Mykhailo-Sichkaruk/PRJ-PENDING-GestureGlove/content/docs/sk/sthdf/ST-029-MarochokYaroslav/index.md

---
title: "ST-029-MarochokYaroslav"
---

# Yaroslav Marochok

Identifikátor v zozname: **ST029**. Tímový projekt: [Gesture Glove](../PRJ-PENDING-GestureGlove/index.md).

- [About Me](./about-me/index.md)
- [Knowledge Contribution (KNIFE)](./knowledge-contribution/index.md)
- [Project Summary](./project-summary/index.md)
- [Project Outcomes](./project-outcomes/index.md)
- [Pitch Presentation](./pitch-presentation/index.md)
- [Final Presentation](./final-presentation/index.md)
- [Reflexia](./reflexia/index.md)

Pripravená štruktúra pre individuálne výstupy. Autor doplní vlastný text; príspevky ani výsledky zatiaľ nie sú deklarované.

GitHub: [ymarochok](https://github.com/ymarochok).
