Mykhailo-Sichkaruk/PRJ-PENDING-GestureGlove/core/templates/content/sthdf/body/index.md

# STHDF — Dashboard

V tejto sekcii sa nachádzajú študentské deliverables.

## 🔗 Navigácia

- **01 – About Me**  
  → [01 – About Me](./students/about-me/index.md)
  
- **02 – Knowledge Contribution (A2)**  
  → [02 – Knowledge Contribution (A2)](./students/knowledge-contribution/index.md)

- **03 – Project Summary**  
  → [03 – Project Summary](./students/project-summary/index.md)

- **04 – Project Outcomes**  
  → [04 – Project Outcomes](./students/project-outcomes/index.md)

- **05 – Pitch Presentation**  
  → [05 – Pitch Presentation](./students/pitch-presentation/index.md)

- **06 – Final Presentation**  
  → [06 – Final Presentation](./students/final-presentation/index.md)

- **07 – Reflexia**  
  → [07 – Reflexia](./students/reflexia/index.md)

---

## ℹ️ Poznámka
Tento súbor je súčasťou *defaultného template* a zabezpečuje stabilitu sidebaru aj navigácie.

## Navigácia
- [↩️ Späť](../../index.md)
- [Projektové rámce — 7Ds, SDLC, Q12](./projects/index.md)
