Mykhailo-Sichkaruk/PRJ-PENDING-GestureGlove/content/docs/en/knifes/knifes_overview/KNIFE_Overview_List.md

---
# 🧩 Versioning – systém dopĺňa automaticky
fm_version: "1.0.1"

# Dátum buildu – generuje skript
fm_build: "{{FM_BUILD}}"

# Poznámka k verzii – voliteľné
fm_version_comment: ""

# 🆔 IDENTITY --------------------------------------------------------

# ID generuje CLI / skript
id: "KNIFE_OVERVIEW_LIST_EN"

# Unikátne UUID – generuje skript
guid: "47377b57-1a6c-4d85-b179-e202dff15484"

# 🧭 CONTEXT ---------------------------------------------------------

# DAO / doména (knife, sdlc, q12, 7ds...) dopĺňa skript
dao: "{{DAO}}"

# Názov zápisu – dopĺňa používateľ
title: "🗂 KNIFE Overview – List"

# Krátky popis – dopĺňa používateľ (voliteľné)
description: "{{DESCRIPTION}}"

# 👥 AUTHORSHIP ------------------------------------------------------

# Hlavný autor – z globálneho configu
author: "Roman Kazička"

# Zoznam autorov – generuje skript
authors:
  - "Roman Kazička"

# 🗂 CLASSIFICATION ---------------------------------------------------

# Nadradená kategória – môže doplniť používateľ
category: ""

# Typ dokumentu (guide, case, tutorial...) – používateľ (voliteľné)
type: ""

# Priorita (low/medium/high) – voliteľné
priority: ""

# Tagy – odporúča sa 2–6 tagov.
# Typy tagov:
#   - rámce: knife, 7ds, sdlc, q12
#   - účel: tutorial, guide, pattern, case-study
#   - téma: git, backup, ai, communication
#   - úroveň: beginner, intermediate, advanced
tags: []

# 🌍 LOCALIZATION -----------------------------------------------------

# Jazyk dokumentu – doplní skript podľa štruktúry
locale: "en"

# 🕒 LIFECYCLE --------------------------------------------------------

# Dátum vytvorenia – generuje skript
created: "2026-10-08"

# Dátum poslednej úpravy – dopĺňa človek
modified: ""

# Stav dokumentu – default "backlog"
status: "backlog"

# Viditeľnosť – default "public"
privacy: "public"

# ⚖ INTELLECTUAL PROPERTY -------------------------------------------

# Držiteľ práv k obsahu – dopĺňa skript
rights_holder_content: "Roman Kazička"

# Systémový vlastník práv
rights_holder_system: "CAA / KNIFE / LetItGrow"

# Licencia
license: "CC-BY-NC-SA-4.0"

# Disclaimer
disclaimer: "Use at your own risk. Methods provided as-is; participation is voluntary and context-aware."

# Copyright
copyright: "© 2025 Roman Kazička"

# 🔗 ORIGIN / PROVENANCE ---------------------------------------------

# Repozitár pôvodu
origin_repo: ""

# URL pôvodného repozitára
origin_repo_url: ""

# Commit pôvodu
origin_commit: ""

# Branch pôvodu
origin_branch: ""

# Systém pôvodu (CAA/KNIFE/STHDF…)
origin_system: "CAA"

# Pôvodný autor
origin_author: "Roman Kazička"

# Importovaný zdroj
origin_imported_from: ""

# Dátum importu
origin_import_date: ""

# 🧱 RESERVED ---------------------------------------------------------

fm_reserved1: ""
fm_reserved2: ""
---

# 🗂 KNIFE Overview – List

<!-- fm-visible: start -->
> **GUID:** `47377b57-1a6c-4d85-b179-e202dff15484`
> **Status:** `backlog` · **Author:** Roman Kazička · **License:** CC-BY-NC-SA-4.0
<!-- fm-visible: end -->

[📰 Blog](./KNIFE_Overview_Blog.md) | **[🗂 List](./KNIFE_Overview_List.md)** | [📊 Details](./KNIFE_Overview_Details.md) | [↩️ KNIFES](../index.md)
