Mykhailo-Sichkaruk/PRJ-PENDING-GestureGlove/content/docs/sk/sthdf/PRJ-PENDING-GestureGlove/projects/sdlc/01-Requirements/index.md

---
# 🧩 Versioning – systém dopĺňa automaticky
fm_version: "1.0.1"

# Dátum buildu – generuje skript
fm_build: "2026-10-08T11:14:47.749154+00:00"

# Poznámka k verzii – voliteľné
fm_version_comment: ""

# 🆔 IDENTITY --------------------------------------------------------

# ID generuje CLI / skript

# Unikátne UUID – generuje skript
guid: "9a84ae6a-37f9-47a1-815a-2adfdcadd318"

# 🧭 CONTEXT ---------------------------------------------------------

# DAO / doména (knife, sdlc, q12, 7ds...) dopĺňa skript
dao: "sthdf"

# Názov zápisu – dopĺňa používateľ
title: "01 Requirements"

# Krátky popis – dopĺňa používateľ (voliteľné)
description: "{{DESCRIPTION}}"

# 👥 AUTHORSHIP ------------------------------------------------------

# Hlavný autor – z globálneho configu
author: "Roman Kazicka"

# Zoznam autorov – generuje skript
authors:
  - "Roman Kazicka"

# 🗂 CLASSIFICATION ---------------------------------------------------

# Nadradená kategória – môže doplniť používateľ
category: ""

# Typ dokumentu (guide, case, tutorial...) – používateľ (voliteľné)
type: ""

# Priorita (low/medium/high) – voliteľné
priority: ""

# Tagy – odporúča sa 2–6 tagov.
# Typy tagov:
#   - rámce: knife, 7ds, sdlc, q12
#   - účel: tutorial, guide, pattern, case-study
#   - téma: git, backup, ai, communication
#   - úroveň: beginner, intermediate, advanced
tags: []

# 🌍 LOCALIZATION -----------------------------------------------------

# Jazyk dokumentu – doplní skript podľa štruktúry
locale: "sk"

# 🕒 LIFECYCLE --------------------------------------------------------

# Dátum vytvorenia – generuje skript
created: "2026-10-08 13:14"

# Dátum poslednej úpravy – dopĺňa človek
modified: "2026-10-08 13:14"

# Stav dokumentu – default "backlog"
status: "backlog"

# Viditeľnosť – default "public"
privacy: "public"

# ⚖ INTELLECTUAL PROPERTY -------------------------------------------

# Držiteľ práv k obsahu – dopĺňa skript
rights_holder_content: "Roman Kazicka"

# Systémový vlastník práv
rights_holder_system: "CAA / KNIFE / LetItGrow"

# Licencia
license: "CC-BY-NC-SA-4.0"

# Disclaimer
disclaimer: "Use at your own risk. Methods provided as-is; participation is voluntary and context-aware."

# Copyright
copyright: "© 2025 Roman Kazicka"

# 🔗 ORIGIN / PROVENANCE ---------------------------------------------

# Repozitár pôvodu
origin_repo: ""

# URL pôvodného repozitára
origin_repo_url: ""

# Commit pôvodu
origin_commit: ""

# Branch pôvodu
origin_branch: ""

# Systém pôvodu (CAA/KNIFE/STHDF…)
origin_system: "CAA"

# Pôvodný autor
origin_author: "Roman Kazicka"

# Importovaný zdroj
origin_imported_from: ""

# Dátum importu
origin_import_date: ""

# 🧱 RESERVED ---------------------------------------------------------

fm_reserved1: ""
fm_reserved2: ""
---

<!-- SDLC_INSTANCE_ID: PRJ-PENDING-GestureGlove -->

# # 01 Requirements

Zachytenie potrieb, cieľov a očakávaní používateľov. Pridaj user stories a nefunkčné požiadavky.

---
**Navigation:** [⬆️ Up](../index.md) · [🏠 Home](../index.md)
