Mykhailo-Sichkaruk/PRJ-PENDING-GestureGlove/content/docs/index.md

---
fm_version: "1.0.1"
fm_build: "2025-10-28T00:00:00Z"
fm_version_comment: "Stabilné ID/slug pre navigáciu (hub + SK + EN)"
id: "KNIFE_HOME"
guid: "4e609387-282e-5744-97f0-e5bb625100ad"
dao: "knife"
title: "KNIFE – Hub"
description: "Vstupná stránka: preklik na SK a EN dokumentáciu."
author: "Roman Kazička"
authors: ["Roman Kazička"]
category: ""
type: ""
priority: "no"
tags: []
locale: "sk"
created: "2025-10-28"
modified: "YYYY-MM-DDTHH:MM:SSZ"
status: "draft"
privacy: "public"
rights_holder_content: "Roman Kazička"
rights_holder_system: "Roman Kazička (CAA/KNIFE/LetItGrow)"
license: "CC-BY-NC-SA-4.0"
disclaimer: "Use at your own risk. Methods provided as-is; participation is voluntary and context-aware."
copyright: "© 2025 Roman Kazička / SystemThinking"
origin_repo: ""
origin_repo_url: ""
origin_commit: ""
origin_system: ""
author_id: ""
author_did: ""
fm_reserved1: ""
fm_reserved2: ""
slug: "/"
sidebar_position: "1"
---
# KNIFE – Hub

Vitaj v KNIFE dokumentácii. Vyber si jazyk:

- 🇸🇰 **Slovensky** → [/sk/](./sk/index.md)
- 🇬🇧 **English** → [/en/](./en/index.md)

## Gesture Glove — SMVIT 2026–2027

- [Tímový projekt](./sk/sthdf/PRJ-PENDING-GestureGlove/index.md)
- [Mykhailo Sichkaruk — ST033](./sk/sthdf/ST-033-SichkarukMykhailo/index.md)
- [Yaroslav Marochok — ST029](./sk/sthdf/ST-029-MarochokYaroslav/index.md)
