Mykhailo-Sichkaruk/PRJ-PENDING-GestureGlove/content/docs/sk/index.md

---
fm_version: "1.0.1"
fm_build: "2025-10-28T00:00:00Z"
fm_version_comment: "Stabilné ID/slug pre navigáciu (hub + SK + EN)"
id: SK_KNIFE_HOME
guid: "7afa4bdc-bb40-490b-8697-c9bf7c3ba848"
dao: "knife"
title: "KNIFE – Prehľad (SK)"
description: "Slovenská domovská stránka dokumentácie KNIFE."
author: "Roman Kazička"
authors: ["Roman Kazička"]
category: ""
type: ""
priority: "no"
tags: []
locale: "sk"
created: "2025-10-28"
modified: "YYYY-MM-DDTHH:MM:SSZ"
status: "draft"
privacy: "public"
rights_holder_content: "Roman Kazička"
rights_holder_system: "Roman Kazička (CAA/KNIFE/LetItGrow)"
license: "CC-BY-NC-SA-4.0"
disclaimer: "Use at your own risk. Methods provided as-is; participation is voluntary and context-aware."
copyright: "© 2025 Roman Kazička / SystemThinking"
origin_repo: ""
origin_repo_url: ""
origin_commit: ""
origin_system: ""
author_id: ""
author_did: ""
fm_reserved1: ""
fm_reserved2: ""
slug: /sk/
sidebar_position: 1
---

# KNIFE – Prehľad (SK)
<!-- fm-visible: start -->
> **GUID:** `7afa4bdc-bb40-490b-8697-c9bf7c3ba848`
> **Status:** `backlog` · **Author:** Roman Kazička · **License:** CC-BY-NC-SA-4.0
<!-- fm-visible: end -->
Toto je hlavná stránka slovenskej dokumentácie.

- 🔪 [KNIFE príspevky](./knifes/index.md)
- ⚙️ [7Ds rámec](./7Ds/index.md)
- 🧱 [SDLC – Framework](./sdlc/index.md)
- 🎯 [Q12 – Framework](./q12/index.md)
- 🏫 [STHDF – Framework](./sthdf/index.md)
- 🧭 [Späť na Hub](../index.md)

## Gesture Glove — SMVIT 2026–2027

- [Tímový projekt](./sthdf/PRJ-PENDING-GestureGlove/index.md)
- [Mykhailo Sichkaruk — ST033](./sthdf/ST-033-SichkarukMykhailo/index.md)
- [Yaroslav Marochok — ST029](./sthdf/ST-029-MarochokYaroslav/index.md)
