Mykhailo-Sichkaruk/PRJ-PENDING-GestureGlove/content/docs/sk/sthdf/index.md

# STHDF-Dashboard

## Gesture Glove — SMVIT 2026–2027

- [Tímový projekt](./PRJ-PENDING-GestureGlove/index.md)
- [Mykhailo Sichkaruk — ST033](./ST-033-SichkarukMykhailo/index.md)
- [Yaroslav Marochok — ST029](./ST-029-MarochokYaroslav/index.md)
