Mykhailo-Sichkaruk/PRJ-PENDING-GestureGlove/content/docs/sk/sthdf/PRJ-PENDING-GestureGlove/index.md

---
# 🧩 Versioning – systém dopĺňa automaticky
fm_version: "1.0.1"

# Dátum buildu – generuje skript
fm_build: "2026-10-08T11:14:47.705837+00:00"

# Poznámka k verzii – voliteľné
fm_version_comment: ""

# 🆔 IDENTITY --------------------------------------------------------

# ID generuje CLI / skript
id: "PRJ-PENDING-GestureGlove"

# Unikátne UUID – generuje skript
guid: "1783b556-7468-4b27-a10c-9eea4736ef01"

# 🧭 CONTEXT ---------------------------------------------------------

# DAO / doména (knife, sdlc, q12, 7ds...) dopĺňa skript
dao: "sthdf"

# Názov zápisu – dopĺňa používateľ
title: "PRJ-PENDING-GestureGlove – Gesture Glove"

# Krátky popis – dopĺňa používateľ (voliteľné)
description: "Semester gesture-glove project; design pending."

# 👥 AUTHORSHIP ------------------------------------------------------

# Hlavný autor – z globálneho configu
author: "Roman Kazicka"

# Zoznam autorov – generuje skript
authors:
  - "Roman Kazicka"

# 🗂 CLASSIFICATION ---------------------------------------------------

# Nadradená kategória – môže doplniť používateľ
category: ""

# Typ dokumentu (guide, case, tutorial...) – používateľ (voliteľné)
type: ""

# Priorita (low/medium/high) – voliteľné
priority: ""

# Tagy – odporúča sa 2–6 tagov.
# Typy tagov:
#   - rámce: knife, 7ds, sdlc, q12
#   - účel: tutorial, guide, pattern, case-study
#   - téma: git, backup, ai, communication
#   - úroveň: beginner, intermediate, advanced
tags: []

# 🌍 LOCALIZATION -----------------------------------------------------

# Jazyk dokumentu – doplní skript podľa štruktúry
locale: "sk"

# 🕒 LIFECYCLE --------------------------------------------------------

# Dátum vytvorenia – generuje skript
created: "2026-10-08 13:14"

# Dátum poslednej úpravy – dopĺňa človek
modified: "2026-10-08 13:14"

# Stav dokumentu – default "backlog"
status: "backlog"

# Viditeľnosť – default "public"
privacy: "public"

# ⚖ INTELLECTUAL PROPERTY -------------------------------------------

# Držiteľ práv k obsahu – dopĺňa skript
rights_holder_content: "Roman Kazicka"

# Systémový vlastník práv
rights_holder_system: "CAA / KNIFE / LetItGrow"

# Licencia
license: "CC-BY-NC-SA-4.0"

# Disclaimer
disclaimer: "Use at your own risk. Methods provided as-is; participation is voluntary and context-aware."

# Copyright
copyright: "© 2025 Roman Kazicka"

# 🔗 ORIGIN / PROVENANCE ---------------------------------------------

# Repozitár pôvodu
origin_repo: ""

# URL pôvodného repozitára
origin_repo_url: ""

# Commit pôvodu
origin_commit: ""

# Branch pôvodu
origin_branch: ""

# Systém pôvodu (CAA/KNIFE/STHDF…)
origin_system: "CAA"

# Pôvodný autor
origin_author: "Roman Kazicka"

# Importovaný zdroj
origin_imported_from: ""

# Dátum importu
origin_import_date: ""

# 🧱 RESERVED ---------------------------------------------------------

fm_reserved1: ""
fm_reserved2: ""
---

# Gesture Glove — projektový dashboard

V tejto sekcii sa nachádzajú študentské deliverables.

## 🔗 Navigácia

- **01 – About Me**  
  → [01 – About Me](./students/about-me/index.md)
  
- **02 – Knowledge Contribution (A2)**  
  → [02 – Knowledge Contribution (A2)](./students/knowledge-contribution/index.md)

- **03 – Project Summary**  
  → [03 – Project Summary](./students/project-summary/index.md)

- **04 – Project Outcomes**  
  → [04 – Project Outcomes](./students/project-outcomes/index.md)

- **05 – Pitch Presentation**  
  → [05 – Pitch Presentation](./students/pitch-presentation/index.md)

- **06 – Final Presentation**  
  → [06 – Final Presentation](./students/final-presentation/index.md)

- **07 – Reflexia**  
  → [07 – Reflexia](./students/reflexia/index.md)

---

## ℹ️ Poznámka
Tento súbor je súčasťou *defaultného template* a zabezpečuje stabilitu sidebaru aj navigácie.

## Navigácia
- [↩️ Späť](../../index.md)

## Gesture Glove — stav projektu

Tím: Mykhailo Sichkaruk (ST033) a Yaroslav Marochok (ST029). Číslo PRJ ešte nebolo pridelené v poskytnutom zozname.

Cieľ: dokončiť semestrálny projekt SMVIT 2026–2027. Rukavica má používať ohybové senzory aj kontaktné plôšky. Existujúce modely sú iba PoC integrácie CAD/AI nástrojov. Výber súčiastok, napájanie, firmware a merania zostávajú otvorené.

- [Mykhailo — individuálne výstupy](../ST-033-SichkarukMykhailo/index.md)
- [Yaroslav — individuálne výstupy](../ST-029-MarochokYaroslav/index.md)

Nižšie uvedené rámce obsahujú šablóny, nie dokončené výstupy. Každý autor doplní vlastný príspevok a dôkazy.

- [Projektové rámce — 7Ds, SDLC, Q12](./projects/index.md)
