Mykhailo-Sichkaruk/PRJ-PENDING-GestureGlove/content/docs/sk/sthdf/PRJ-PENDING-GestureGlove/students/index.md

---
# 🧩 Versioning – systém dopĺňa automaticky
fm_version: "1.0.1"

# Dátum buildu – generuje skript
fm_build: "2026-10-08T11:14:47.707477+00:00"

# Poznámka k verzii – voliteľné
fm_version_comment: ""

# 🆔 IDENTITY --------------------------------------------------------

# ID generuje CLI / skript

# Unikátne UUID – generuje skript
guid: "cd1e4bc1-3fff-4c71-a971-9ba71dad430e"

# 🧭 CONTEXT ---------------------------------------------------------

# DAO / doména (knife, sdlc, q12, 7ds...) dopĺňa skript
dao: "sthdf"

# Názov zápisu – dopĺňa používateľ
title: "students"

# Krátky popis – dopĺňa používateľ (voliteľné)
description: "{{DESCRIPTION}}"

# 👥 AUTHORSHIP ------------------------------------------------------

# Hlavný autor – z globálneho configu
author: "Roman Kazicka"

# Zoznam autorov – generuje skript
authors:
  - "Roman Kazicka"

# 🗂 CLASSIFICATION ---------------------------------------------------

# Nadradená kategória – môže doplniť používateľ
category: ""

# Typ dokumentu (guide, case, tutorial...) – používateľ (voliteľné)
type: ""

# Priorita (low/medium/high) – voliteľné
priority: ""

# Tagy – odporúča sa 2–6 tagov.
# Typy tagov:
#   - rámce: knife, 7ds, sdlc, q12
#   - účel: tutorial, guide, pattern, case-study
#   - téma: git, backup, ai, communication
#   - úroveň: beginner, intermediate, advanced
tags: []

# 🌍 LOCALIZATION -----------------------------------------------------

# Jazyk dokumentu – doplní skript podľa štruktúry
locale: "sk"

# 🕒 LIFECYCLE --------------------------------------------------------

# Dátum vytvorenia – generuje skript
created: "2026-10-08 13:14"

# Dátum poslednej úpravy – dopĺňa človek
modified: "2026-10-08 13:14"

# Stav dokumentu – default "backlog"
status: "backlog"

# Viditeľnosť – default "public"
privacy: "public"

# ⚖ INTELLECTUAL PROPERTY -------------------------------------------

# Držiteľ práv k obsahu – dopĺňa skript
rights_holder_content: "Roman Kazicka"

# Systémový vlastník práv
rights_holder_system: "CAA / KNIFE / LetItGrow"

# Licencia
license: "CC-BY-NC-SA-4.0"

# Disclaimer
disclaimer: "Use at your own risk. Methods provided as-is; participation is voluntary and context-aware."

# Copyright
copyright: "© 2025 Roman Kazicka"

# 🔗 ORIGIN / PROVENANCE ---------------------------------------------

# Repozitár pôvodu
origin_repo: ""

# URL pôvodného repozitára
origin_repo_url: ""

# Commit pôvodu
origin_commit: ""

# Branch pôvodu
origin_branch: ""

# Systém pôvodu (CAA/KNIFE/STHDF…)
origin_system: "CAA"

# Pôvodný autor
origin_author: "Roman Kazicka"

# Importovaný zdroj
origin_imported_from: ""

# Dátum importu
origin_import_date: ""

# 🧱 RESERVED ---------------------------------------------------------

fm_reserved1: ""
fm_reserved2: ""
---

<!-- SDLC_INSTANCE_ID: PRJ-PENDING-GestureGlove -->

# 👥 Moje deliverables

Toto je rozcestník k tvojim povinným výstupom pre tento predmet.

## Navigácia
- 🧑‍🎓 [About Me](./about-me/index.md)
- 🧩 [Knowledge Contribution](./knowledge-contribution/index.md)
- 🧭 [Project Summary](./project-summary/index.md)
- 🏁 [Project Outcomes](./project-outcomes/index.md)
- 🎤 [Pitch Presentation](./pitch-presentation/index.md)
- 🎬 [Final Presentation](./final-presentation/index.md)
- 🪞 [Reflexia](./reflexia/index.md)

> ℹ️ Poznámka k **Knowledge Contribution**: toto deliverable je v systéme
> reprezentované ako **KNIFE** (štandardná šablóna KNIFE s vlastným FM a
> procesom) — podľa pokynov kurzu.

## Rýchly checklist
- [ ] About Me vyplnené
- [ ] Knowledge Contribution (KNIFE) publikované / referencované
- [ ] Project Summary schválené vyučujúcim
- [ ] Project Outcomes doplnené o odkazy (repo, video, demo)
- [ ] Pitch hotový (5–7 min)
- [ ] Finálna prezentácia hotová (10–12 min)
- [ ] Reflexia pridaná

## Ako pracovať (mini-návod)
1. Otvor príslušnú stránku vyššie a doplň obsah.
2. Pridaj odkazy na repozitár, video a demo (ak máš).
3. Ulož zmeny, commitni a pushni:
   ```bash
   git add .
   git commit -m "Update deliverables"
   git push
   ```

## Navigácia
- [↩️ Späť](../../index.md)
