Mykhailo-Sichkaruk/PRJ-PENDING-GestureGlove/content/docs/sk/sthdf/ST-029-MarochokYaroslav/project-summary/index.md

---
# 🧩 Versioning – systém dopĺňa automaticky
fm_version: "1.0.1"

# Dátum buildu – generuje skript
fm_build: "2026-10-08T11:14:47.708760+00:00"

# Poznámka k verzii – voliteľné
fm_version_comment: ""

# 🆔 IDENTITY --------------------------------------------------------

# ID generuje CLI / skript

# Unikátne UUID – generuje skript

# 🧭 CONTEXT ---------------------------------------------------------

# DAO / doména (knife, sdlc, q12, 7ds...) dopĺňa skript
dao: "sthdf"

# Názov zápisu – dopĺňa používateľ
title: "project summary"

# Krátky popis – dopĺňa používateľ (voliteľné)
description: "{{DESCRIPTION}}"

# 👥 AUTHORSHIP ------------------------------------------------------

# Hlavný autor – z globálneho configu
author: "Roman Kazicka"

# Zoznam autorov – generuje skript
authors:
  - "Roman Kazicka"

# 🗂 CLASSIFICATION ---------------------------------------------------

# Nadradená kategória – môže doplniť používateľ
category: ""

# Typ dokumentu (guide, case, tutorial...) – používateľ (voliteľné)
type: ""

# Priorita (low/medium/high) – voliteľné
priority: ""

# Tagy – odporúča sa 2–6 tagov.
# Typy tagov:
#   - rámce: knife, 7ds, sdlc, q12
#   - účel: tutorial, guide, pattern, case-study
#   - téma: git, backup, ai, communication
#   - úroveň: beginner, intermediate, advanced
tags: []

# 🌍 LOCALIZATION -----------------------------------------------------

# Jazyk dokumentu – doplní skript podľa štruktúry
locale: "sk"

# 🕒 LIFECYCLE --------------------------------------------------------

# Dátum vytvorenia – generuje skript
created: "2026-10-08 13:14"

# Dátum poslednej úpravy – dopĺňa človek
modified: "2026-10-08 13:14"

# Stav dokumentu – default "backlog"
status: "backlog"

# Viditeľnosť – default "public"
privacy: "public"

# ⚖ INTELLECTUAL PROPERTY -------------------------------------------

# Držiteľ práv k obsahu – dopĺňa skript
rights_holder_content: "Roman Kazicka"

# Systémový vlastník práv
rights_holder_system: "CAA / KNIFE / LetItGrow"

# Licencia
license: "CC-BY-NC-SA-4.0"

# Disclaimer
disclaimer: "Use at your own risk. Methods provided as-is; participation is voluntary and context-aware."

# Copyright
copyright: "© 2025 Roman Kazicka"

# 🔗 ORIGIN / PROVENANCE ---------------------------------------------

# Repozitár pôvodu
origin_repo: ""

# URL pôvodného repozitára
origin_repo_url: ""

# Commit pôvodu
origin_commit: ""

# Branch pôvodu
origin_branch: ""

# Systém pôvodu (CAA/KNIFE/STHDF…)
origin_system: "CAA"

# Pôvodný autor
origin_author: "Roman Kazicka"

# Importovaný zdroj
origin_imported_from: ""

# Dátum importu
origin_import_date: ""

# 🧱 RESERVED ---------------------------------------------------------

fm_reserved1: ""
fm_reserved2: ""
---

<!-- SDLC_INSTANCE_ID: PRJ-PENDING-GestureGlove -->

# 📝 Project Summary

## 🔖 Identifikácia
## 1️⃣ Názov projektu
*(Jasný, výstižný, inšpiratívny – ako by sa mal objaviť na plagáte.)*
- **Názov projektu:** `PRJ_XXX_<Názov>_<ST_XXX>_<ST_XXX>`
- **Stručný popis:** 2–3 vety

## 2️⃣ Členovia tímu

| ST ID | Meno | Rola v tíme | Kompetencie |
|---|---|---|---|
| ST001 | | Project Lead | koordinácia |
| ST002 | | Developer | implementácia |
| ST003 | | Designer | UI/UX |

## 3️⃣ Motivácia tímu
- Prečo ste si vybrali tento projekt?
- Aký osobný alebo profesný zmysel má pre vás riešenie tejto témy?
- Prečo je projekt dôležitý
- Aký problém rieši

## 4️⃣ Cieľ a pridaná hodnota projektu
- Aký je finálny cieľ
- Ako spoznáme, že projekt je úspešný

## 5️⃣ Popis riešenia
- Stručne opíšte architektúru, nástroje a technológie, ktoré použijete.
- Zamerajte sa na **"čo"** riešite, nie ešte "ako".

## 6️⃣ Projektový plán
- Odhadovaný čas na prácu: _x hodín / týždeň_
- Predpokladaný stav v čase prezentácie: _MVP / prototyp / dokumentácia / funkčný produkt_
- Hlavné míľniky:
  - [ ] Príprava
  - [ ] Implementácia
  - [ ] Testovanie
  - [ ] Prezentácia

### 📅 Míľniky a výstupy
- **Do januára dodáme:**
  - [ ] prototyp
  - [ ] prezentáciu
  - [ ] dokumentáciu

## 7️⃣ Zákazník a hodnoty
- Kto by mohol byť používateľom projektu?
- Čo mu to prinesie?

## 8️⃣ Očakávané výstupy
- Dokumentácia: (napr. README, KNIFE článok, demo stránka...)
- Artefakty: (napr. prototyp, appka, vizualizácia...)

## 📚 Kontext
- KNIFE príspevky, literatúra, inšpirácie

## 🧭 Riziká a závislosti
- Riziká projektu
- Na čom závisí

## 9️⃣ Reflexia a ďalšie kroky
Čo očakávate, že sa naučíte?
Ako by sa projekt mohol rozvíjať ďalej?

---

## Navigácia
- [↩️ Späť](../index.md)

## Stav — Yaroslav Marochok

Čaká na doplnenie autorom. Táto stránka je šablóna, nie odovzdaný výstup.
