Mykhailo-Sichkaruk/PRJ-PENDING-GestureGlove/content/docs/sk/sthdf/PRJ-PENDING-GestureGlove/projects/7ds/index.md

---
# 🧩 Versioning – systém dopĺňa automaticky
fm_version: "1.0.1"

# Dátum buildu – generuje skript
fm_build: "2026-10-08T11:14:47.715319+00:00"

# Poznámka k verzii – voliteľné
fm_version_comment: ""

# 🆔 IDENTITY --------------------------------------------------------

# ID generuje CLI / skript

# Unikátne UUID – generuje skript
guid: "621051e8-e44d-4a40-b3c1-78eab780dd28"

# 🧭 CONTEXT ---------------------------------------------------------

# DAO / doména (knife, sdlc, q12, 7ds...) dopĺňa skript
dao: "sthdf"

# Názov zápisu – dopĺňa používateľ
title: "7ds"

# Krátky popis – dopĺňa používateľ (voliteľné)
description: "{{DESCRIPTION}}"

# 👥 AUTHORSHIP ------------------------------------------------------

# Hlavný autor – z globálneho configu
author: "Roman Kazicka"

# Zoznam autorov – generuje skript
authors:
  - "Roman Kazicka"

# 🗂 CLASSIFICATION ---------------------------------------------------

# Nadradená kategória – môže doplniť používateľ
category: ""

# Typ dokumentu (guide, case, tutorial...) – používateľ (voliteľné)
type: ""

# Priorita (low/medium/high) – voliteľné
priority: ""

# Tagy – odporúča sa 2–6 tagov.
# Typy tagov:
#   - rámce: knife, 7ds, sdlc, q12
#   - účel: tutorial, guide, pattern, case-study
#   - téma: git, backup, ai, communication
#   - úroveň: beginner, intermediate, advanced
tags: []

# 🌍 LOCALIZATION -----------------------------------------------------

# Jazyk dokumentu – doplní skript podľa štruktúry
locale: "sk"

# 🕒 LIFECYCLE --------------------------------------------------------

# Dátum vytvorenia – generuje skript
created: "2026-10-08 13:14"

# Dátum poslednej úpravy – dopĺňa človek
modified: "2026-10-08 13:14"

# Stav dokumentu – default "backlog"
status: "backlog"

# Viditeľnosť – default "public"
privacy: "public"

# ⚖ INTELLECTUAL PROPERTY -------------------------------------------

# Držiteľ práv k obsahu – dopĺňa skript
rights_holder_content: "Roman Kazicka"

# Systémový vlastník práv
rights_holder_system: "CAA / KNIFE / LetItGrow"

# Licencia
license: "CC-BY-NC-SA-4.0"

# Disclaimer
disclaimer: "Use at your own risk. Methods provided as-is; participation is voluntary and context-aware."

# Copyright
copyright: "© 2025 Roman Kazicka"

# 🔗 ORIGIN / PROVENANCE ---------------------------------------------

# Repozitár pôvodu
origin_repo: ""

# URL pôvodného repozitára
origin_repo_url: ""

# Commit pôvodu
origin_commit: ""

# Branch pôvodu
origin_branch: ""

# Systém pôvodu (CAA/KNIFE/STHDF…)
origin_system: "CAA"

# Pôvodný autor
origin_author: "Roman Kazicka"

# Importovaný zdroj
origin_imported_from: ""

# Dátum importu
origin_import_date: ""

# 🧱 RESERVED ---------------------------------------------------------

fm_reserved1: ""
fm_reserved2: ""
---

<!-- SDLC_INSTANCE_ID: PRJ-PENDING-GestureGlove -->

# 7Ds – Navigačný rozcestník

Tento priečinok predstavuje základnú **kostru frameworku 7Ds** –  
od riadenia a motivácie až po poučenia a zdroje.

Každá disciplína má vlastný priečinok s `index.md` a podpriečinkami pre jednotlivé oblasti.  
Použi túto mapu ako hlavný navigačný prehľad celého SDLC / 7Ds cyklu.

---

## 📂 Hlavné disciplíny

| # | Disciplína | Popis |
|---|---|---|
| 1️⃣ | [**D1 – Management**](./01.D1-Management/index.md) | Ciele, plány, rozhodnutia a evidencia práce. |
| 2️⃣ | [**D2 – Motivation**](./02.D2-Motivation/index.md) | Stakeholderi, dôvody, vízia a hnacia sila projektu. |
| 3️⃣ | [**D3 – Analysis**](./03.D3-Analysis/index.md) | Zdroje, analýzy, vstupy a východiská riešenia. |
| 4️⃣ | [**D4 – Design**](./04.D4-Design/index.md) | Návrh architektúry, procesov, komponentov a vizuálov. |
| 5️⃣ | [**D5 – Implementation**](./05.D5-Implementation/index.md) | Realizácia návrhu, vývoj a integrácia riešenia. |
| 6️⃣ | [**D6 – Verification & Testing**](./06.D6-Verification-Testing/index.md) | Overenie kvality a testovanie riešenia. |
| 7️⃣ | [**D7 – Lessons Learned**](./07.D7-LessonLearned/index.md) | Získané poznatky, odporúčania a spätná väzba. |

---

## 🧩 Doplnkové sekcie

- [00.Navigations](./00.Navigations/index.md) – centrálna mapa s odkazmi naprieč dokumentáciou.  
- [Docusaurus Guide](./01.D1-Management/02.Strategy/Docusaurus-Guide/Guide_Intro.md) – odporúčania pre písanie dokumentácie.  
- [HowTo a Troubleshooting](./07.D7-LessonLearned/06.HowTo/index.md) – praktické mini-návody.  

---

**Navigation:** [🏠 Home](../index.md)
