Mykhailo-Sichkaruk/PRJ-PENDING-GestureGlove/content/docs/sk/sthdf/PRJ-PENDING-GestureGlove/projects/sdlc/index.md

---
# 🧩 Versioning – systém dopĺňa automaticky
fm_version: "1.0.1"

# Dátum buildu – generuje skript
fm_build: "2026-10-08T11:14:47.713200+00:00"

# Poznámka k verzii – voliteľné
fm_version_comment: ""

# 🆔 IDENTITY --------------------------------------------------------

# ID generuje CLI / skript

# Unikátne UUID – generuje skript
guid: "9cf202c7-ca57-4d27-b4ca-aa5742fce11b"

# 🧭 CONTEXT ---------------------------------------------------------

# DAO / doména (knife, sdlc, q12, 7ds...) dopĺňa skript
dao: "sthdf"

# Názov zápisu – dopĺňa používateľ
title: "sdlc"

# Krátky popis – dopĺňa používateľ (voliteľné)
description: "{{DESCRIPTION}}"

# 👥 AUTHORSHIP ------------------------------------------------------

# Hlavný autor – z globálneho configu
author: "Roman Kazicka"

# Zoznam autorov – generuje skript
authors:
  - "Roman Kazicka"

# 🗂 CLASSIFICATION ---------------------------------------------------

# Nadradená kategória – môže doplniť používateľ
category: ""

# Typ dokumentu (guide, case, tutorial...) – používateľ (voliteľné)
type: ""

# Priorita (low/medium/high) – voliteľné
priority: ""

# Tagy – odporúča sa 2–6 tagov.
# Typy tagov:
#   - rámce: knife, 7ds, sdlc, q12
#   - účel: tutorial, guide, pattern, case-study
#   - téma: git, backup, ai, communication
#   - úroveň: beginner, intermediate, advanced
tags: []

# 🌍 LOCALIZATION -----------------------------------------------------

# Jazyk dokumentu – doplní skript podľa štruktúry
locale: "sk"

# 🕒 LIFECYCLE --------------------------------------------------------

# Dátum vytvorenia – generuje skript
created: "2026-10-08 13:14"

# Dátum poslednej úpravy – dopĺňa človek
modified: "2026-10-08 13:14"

# Stav dokumentu – default "backlog"
status: "backlog"

# Viditeľnosť – default "public"
privacy: "public"

# ⚖ INTELLECTUAL PROPERTY -------------------------------------------

# Držiteľ práv k obsahu – dopĺňa skript
rights_holder_content: "Roman Kazicka"

# Systémový vlastník práv
rights_holder_system: "CAA / KNIFE / LetItGrow"

# Licencia
license: "CC-BY-NC-SA-4.0"

# Disclaimer
disclaimer: "Use at your own risk. Methods provided as-is; participation is voluntary and context-aware."

# Copyright
copyright: "© 2025 Roman Kazicka"

# 🔗 ORIGIN / PROVENANCE ---------------------------------------------

# Repozitár pôvodu
origin_repo: ""

# URL pôvodného repozitára
origin_repo_url: ""

# Commit pôvodu
origin_commit: ""

# Branch pôvodu
origin_branch: ""

# Systém pôvodu (CAA/KNIFE/STHDF…)
origin_system: "CAA"

# Pôvodný autor
origin_author: "Roman Kazicka"

# Importovaný zdroj
origin_imported_from: ""

# Dátum importu
origin_import_date: ""

# 🧱 RESERVED ---------------------------------------------------------

fm_reserved1: ""
fm_reserved2: ""
---

<!-- SDLC_INSTANCE_ID: PRJ-PENDING-GestureGlove -->

# 🧭 Project Summary – SDLC v9 (Full Lifecycle)

Tento priečinok obsahuje **9 etáp SDLC** – od požiadaviek po riadenie zmien.  
Každá fáza má vlastný `index.md` so stručným opisom a úlohami.

---

## 📂 Etapy SDLC

1️⃣ [**Requirements**](./01-Requirements/index.md) – Zachytenie potrieb, cieľov a očakávaní používateľov.  
2️⃣ [**Analysis**](./02-Analysis/index.md) – Analýza uskutočniteľnosti, rizík a alternatív riešenia.  
3️⃣ [**Design**](./03-Design/index.md) – Návrh architektúry, dátového modelu a UI/UX.  
4️⃣ [**Implementation**](./04-Implementation/index.md) – Realizácia návrhu – kód, konfigurácia, build pipeline.  
5️⃣ [**Testing**](./05-Testing/index.md) – Overenie kvality – test cases, QA checklist, výsledky.  
6️⃣ [**Deployment**](./06-Deployment/index.md) – Nasadenie riešenia, demo alebo prezentácia MVP.  
7️⃣ [**Maintenance**](./07-Maintenance/index.md) – Údržba a drobné vylepšenia po nasadení.  
8️⃣ [**Documentation**](./08-Documentation/index.md) – Používateľská a technická dokumentácia.  
9️⃣ [**Change Management**](./09-ChangeManagement/index.md) – Riadenie zmien – Change Log, Impact Analysis, CR.

---

**Navigation:** [🏠 Home](../index.md) · Otvor niektorú z podpriečinkov ↑
