Mykhailo-Sichkaruk/PRJ-PENDING-GestureGlove/examples/poc/cad/glove-poc-palm.png

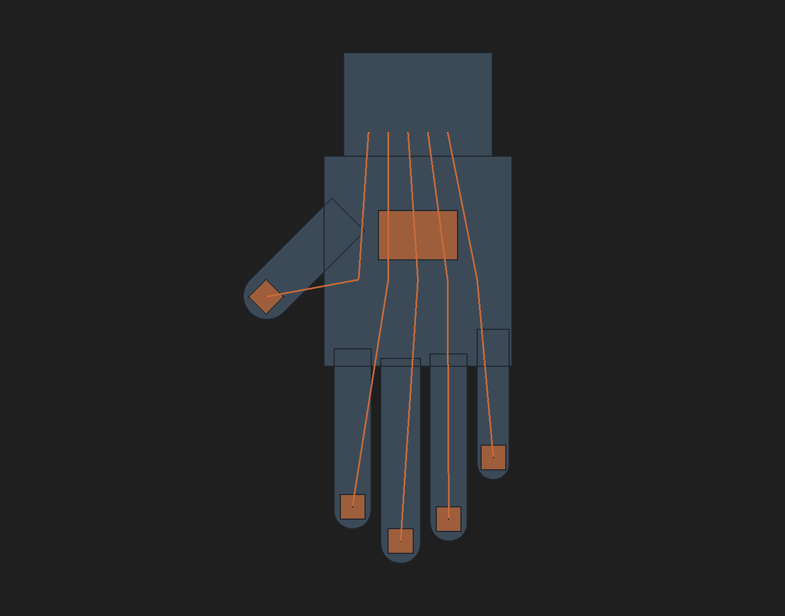
examples/poc/cad/glove-poc-palm.png
