Mykhailo-Sichkaruk/PRJ-PENDING-GestureGlove/examples/poc/cad/glove-poc.png

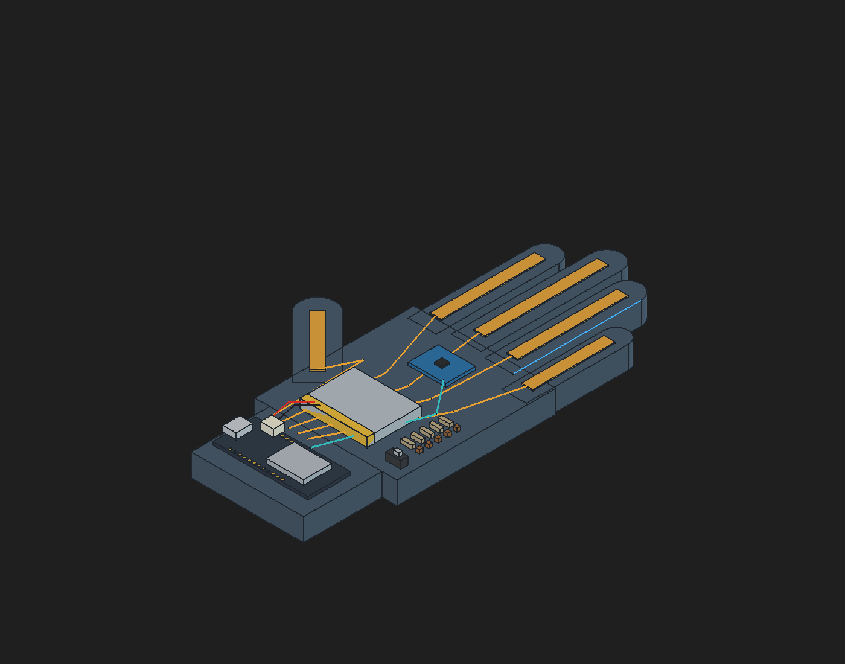
examples/poc/cad/glove-poc.png
