Mykhailo-Sichkaruk/PRJ-PENDING-GestureGlove/examples/poc/electronics/glove/gesture-glove-v2.kicad_sch

## KiCad design examples/poc/electronics/glove/gesture-glove-v2.kicad_sch (2026-10-08)

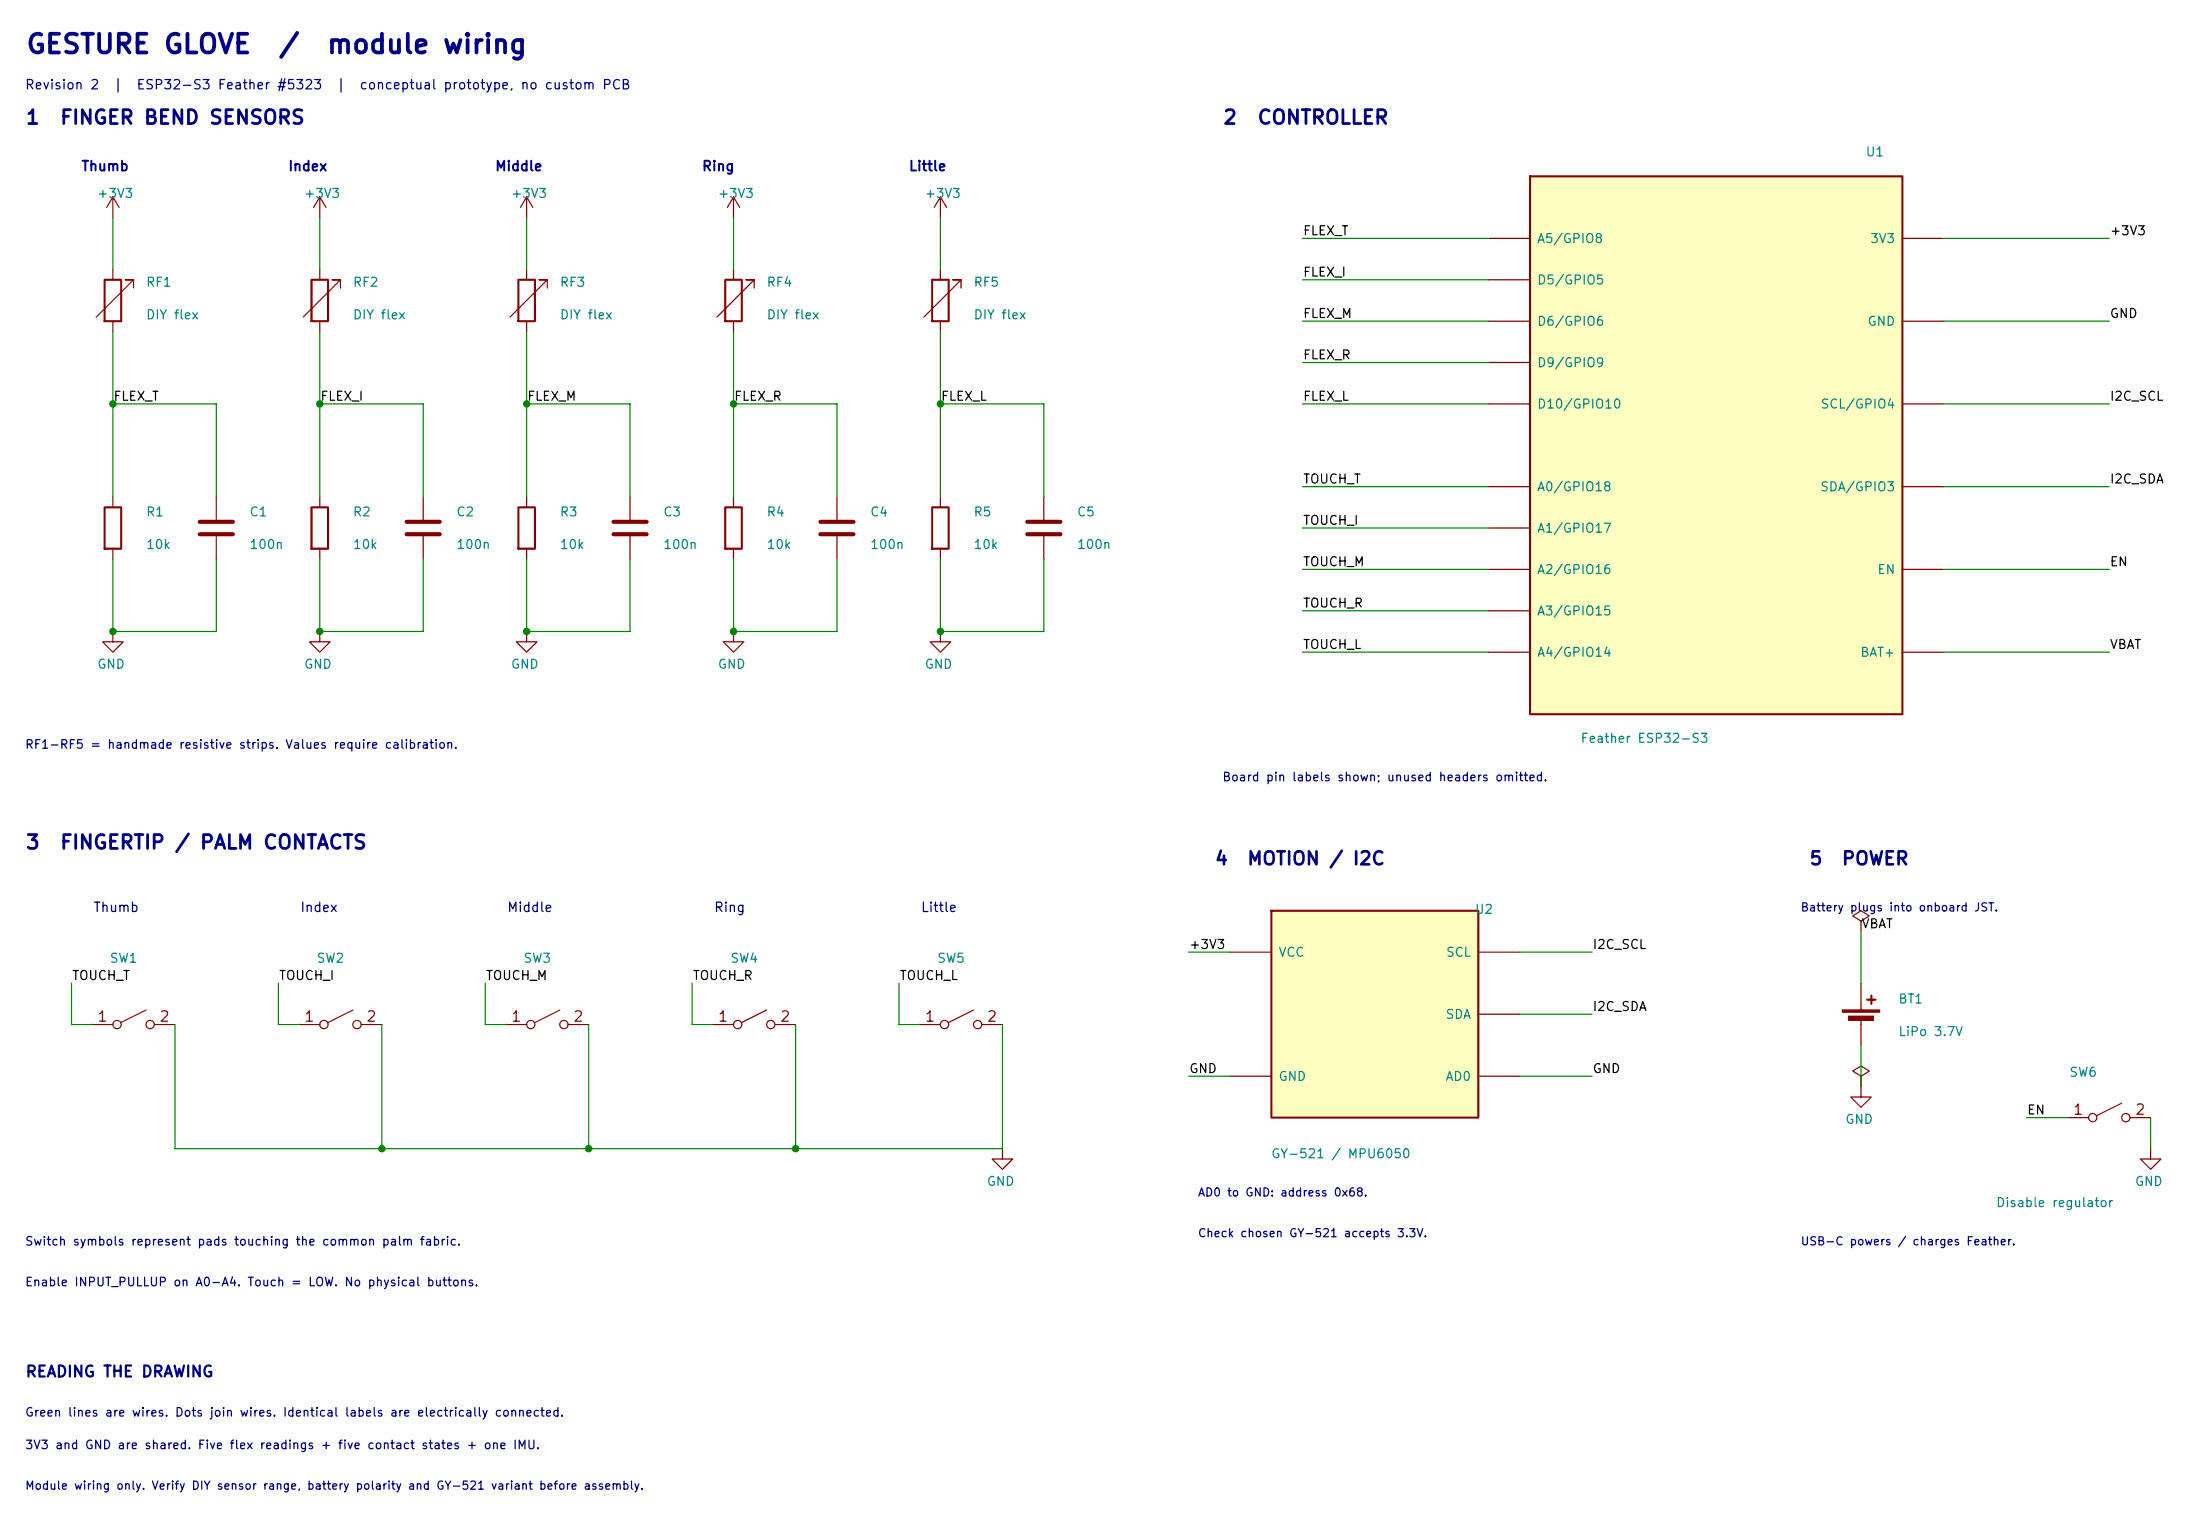
[picture p40: schematic gesture-glove-v2.kicad_sch]

Parts:
BT1: LiPo 3.7V
C1, C2, C3, C4, C5: 100n
R1, R2, R3, R4, R5: 10k
RF1, RF2, RF3, RF4, RF5: DIY flex
SW1, SW2, SW3, SW4, SW5: Pad contact
SW6: Disable regulator
U1: Feather ESP32-S3
U2: GY-521 / MPU6050

Connections:
+3V3: RF1.1, RF2.1, RF3.1, RF4.1, RF5.1, U1.3V3, U2.1 (VCC)
EN: SW6.1 (A), U1.EN
FLEX_I: C2.1, R2.1, RF2.2, U1.D5 (D5/GPIO5)
FLEX_L: C5.1, R5.1, RF5.2, U1.D10 (D10/GPIO10)
FLEX_M: C3.1, R3.1, RF3.2, U1.D6 (D6/GPIO6)
FLEX_R: C4.1, R4.1, RF4.2, U1.D9 (D9/GPIO9)
FLEX_T: C1.1, R1.1, RF1.2, U1.A5 (A5/GPIO8)
GND: BT1.2 (-), C1.2, C2.2, C3.2, C4.2, C5.2, R1.2, R2.2, R3.2, R4.2, R5.2, SW1.2 (B), SW2.2 (B), SW3.2 (B), SW4.2 (B), SW5.2 (B), SW6.2 (B), U1.GND, U2.2 (GND), U2.7 (AD0)
I2C_SCL: U1.SCL (SCL/GPIO4), U2.3 (SCL)
I2C_SDA: U1.SDA (SDA/GPIO3), U2.4 (SDA)
TOUCH_I: SW2.1 (A), U1.A1 (A1/GPIO17)
TOUCH_L: SW5.1 (A), U1.A4 (A4/GPIO14)
TOUCH_M: SW3.1 (A), U1.A2 (A2/GPIO16)
TOUCH_R: SW4.1 (A), U1.A3 (A3/GPIO15)
TOUCH_T: SW1.1 (A), U1.A0 (A0/GPIO18)
VBAT: BT1.1 (+), U1.BAT (BAT+)

Notes on the sheet:
RF1-RF5 = handmade resistive strips. Values require calibration.
Check chosen GY-521 accepts 3.3V.
Little
Thumb
Enable INPUT_PULLUP on A0-A4. Touch = LOW. No physical buttons.
Ring
Index
5 POWER
Board pin labels shown; unused headers omitted.
Module wiring only. Verify DIY sensor range, battery polarity and GY-521 variant before assembly.
3 FINGERTIP / PALM CONTACTS
4 MOTION / I2C
Switch symbols represent pads touching the common palm fabric.
3V3 and GND are shared. Five flex readings + five contact states + one IMU.
Revision 2 | ESP32-S3 Feather #5323 | conceptual prototype, no custom PCB
AD0 to GND: address 0x68.
Green lines are wires. Dots join wires. Identical labels are electrically connected.
USB-C powers / charges Feather.
Middle
2 CONTROLLER
READING THE DRAWING
Battery plugs into onboard JST.
GESTURE GLOVE / module wiring
1 FINGER BEND SENSORS
