Mykhailo-Sichkaruk/PRJ-PENDING-GestureGlove/examples/poc/electronics/glove/gesture-glove.kicad_sch

## KiCad design examples/poc/electronics/glove/gesture-glove.kicad_sch (2026-10-08)

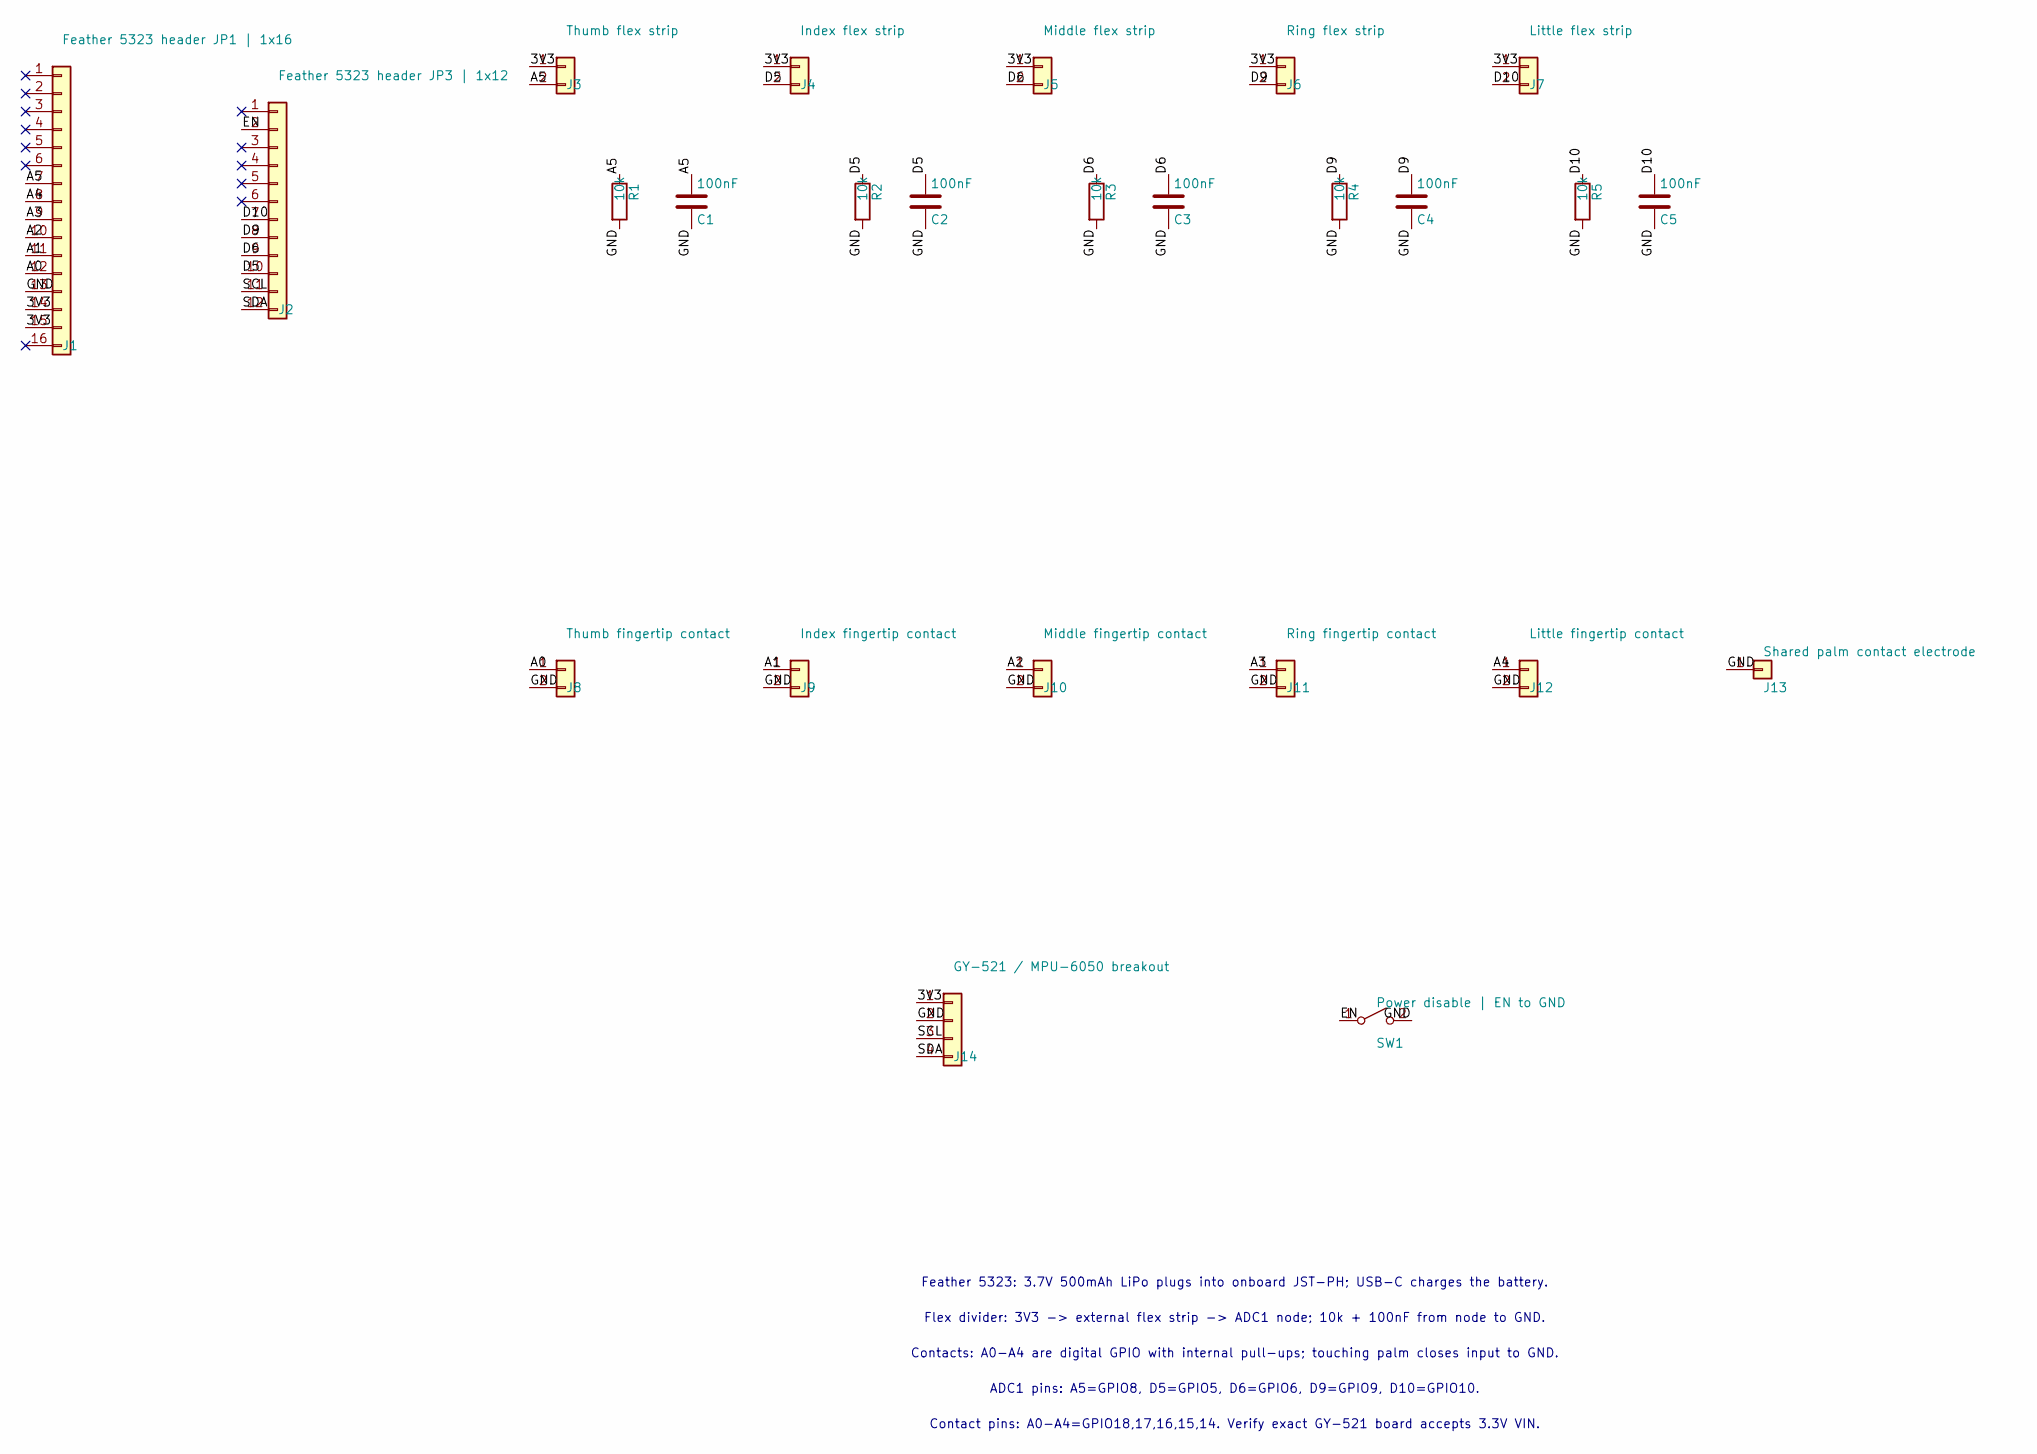
[picture p41: schematic gesture-glove.kicad_sch]

Parts:
C1, C2, C3, C4, C5: 100nF; C_Disc_D5.0mm_W2.5mm_P5.00mm
J1: Feather 5323 header JP1 | 1x16
J2: Feather 5323 header JP3 | 1x12
J3: Thumb flex strip
J4: Index flex strip
J5: Middle flex strip
J6: Ring flex strip
J7: Little flex strip
J8: Thumb fingertip contact
J9: Index fingertip contact
J10: Middle fingertip contact
J11: Ring fingertip contact
J12: Little fingertip contact
J13: Shared palm contact electrode
J14: GY-521 / MPU-6050 breakout
R1, R2, R3, R4, R5: 10k; R_Axial_DIN0207_L6.3mm_D2.5mm_P10.16mm_Horizontal
SW1: Power disable | EN to GND

Connections:
3V3: J1.14, J1.15, J3.1, J4.1, J5.1, J6.1, J7.1, J14.1
A0: J1.12, J8.1
A1: J1.11, J9.1
A2: J1.10, J10.1
A3: J1.9, J11.1
A4: J1.8, J12.1
A5: C1.1, J1.7, J3.2, R1.1
D5: C2.1, J2.10, J4.2, R2.1
D6: C3.1, J2.9, J5.2, R3.1
D9: C4.1, J2.8, J6.2, R4.1
D10: C5.1, J2.7, J7.2, R5.1
EN: J2.2, SW1.1 (A)
GND: C1.2, C2.2, C3.2, C4.2, C5.2, J1.13, J8.2, J9.2, J10.2, J11.2, J12.2, J13.1, J14.2, R1.2, R2.2, R3.2, R4.2, R5.2, SW1.2 (B)
SCL: J2.11, J14.3
SDA: J2.12, J14.4

Notes on the sheet:
Contact pins: A0-A4=GPIO18,17,16,15,14. Verify exact GY-521 board accepts 3.3V VIN.
Contacts: A0-A4 are digital GPIO with internal pull-ups; touching palm closes input to GND.
Feather 5323: 3.7V 500mAh LiPo plugs into onboard JST-PH; USB-C charges the battery.
Flex divider: 3V3 -> external flex strip -> ADC1 node; 10k + 100nF from node to GND.
ADC1 pins: A5=GPIO8, D5=GPIO5, D6=GPIO6, D9=GPIO9, D10=GPIO10.
